twisterss/CadreCouleurs/tools/color_loader/color_loader.ino

// Simple sketch to write
// a list of colors in the EEPROM
// The list is generated in Python
#include <EEPROM.h>

#define COLOR_HUES 85
#define COLOR_SATS 4

uint8_t colors[COLOR_HUES*COLOR_SATS][3] = {{255, 127, 127}, {255, 85, 85}, {255, 42, 42}, {255, 0, 0}, {255, 136, 127}, {255, 97, 85}, {255, 57, 42}, {255, 17, 0}, {255, 145, 127}, {255, 109, 85}, {255, 72, 42}, {255, 35, 0}, {255, 154, 127}, {255, 121, 85}, {255, 87, 42}, {255, 54, 0}, {255, 163, 127}, {255, 133, 85}, {255, 102, 42}, {255, 72, 0}, {255, 172, 127}, {255, 145, 85}, {255, 117, 42}, {255, 89, 0}, {255, 181, 127}, {255, 157, 85}, {255, 132, 42}, {255, 108, 0}, {255, 190, 127}, {255, 169, 85}, {255, 147, 42}, {255, 126, 0}, {255, 199, 127}, {255, 181, 85}, {255, 162, 42}, {255, 144, 0}, {255, 208, 127}, {255, 193, 85}, {255, 177, 42}, {255, 162, 0}, {255, 217, 127}, {255, 205, 85}, {255, 192, 42}, {255, 179, 0}, {255, 226, 127}, {255, 217, 85}, {255, 207, 42}, {255, 198, 0}, {255, 235, 127}, {255, 229, 85}, {255, 222, 42}, {255, 216, 0}, {255, 244, 127}, {255, 241, 85}, {255, 237, 42}, {255, 234, 0}, {255, 253, 127}, {255, 253, 85}, {255, 252, 42}, {255, 252, 0}, {247, 255, 127}, {245, 255, 85}, {242, 255, 42}, {240, 255, 0}, {238, 255, 127}, {233, 255, 85}, {227, 255, 42}, {222, 255, 0}, {229, 255, 127}, {220, 255, 85}, {212, 255, 42}, {203, 255, 0}, {220, 255, 127}, {209, 255, 85}, {197, 255, 42}, {186, 255, 0}, {211, 255, 127}, {196, 255, 85}, {182, 255, 42}, {167, 255, 0}, {202, 255, 127}, {185, 255, 85}, {167, 255, 42}, {150, 255, 0}, {193, 255, 127}, {173, 255, 85}, {152, 255, 42}, {131, 255, 0}, {184, 255, 127}, {160, 255, 85}, {137, 255, 42}, {113, 255, 0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

void setup() {
  for (uint16_t color = 0; color < COLOR_HUES*COLOR_SATS; color++) {
    for (uint8_t comp = 0; comp < 3; comp++) {
      EEPROM.write(color*3 + comp, colors[color][comp]);
    }
  }

}

void loop() {
  // nothing to do
}
